HandHeldLegend/HHL-GameCube-Parts/Triggers/Front View.png

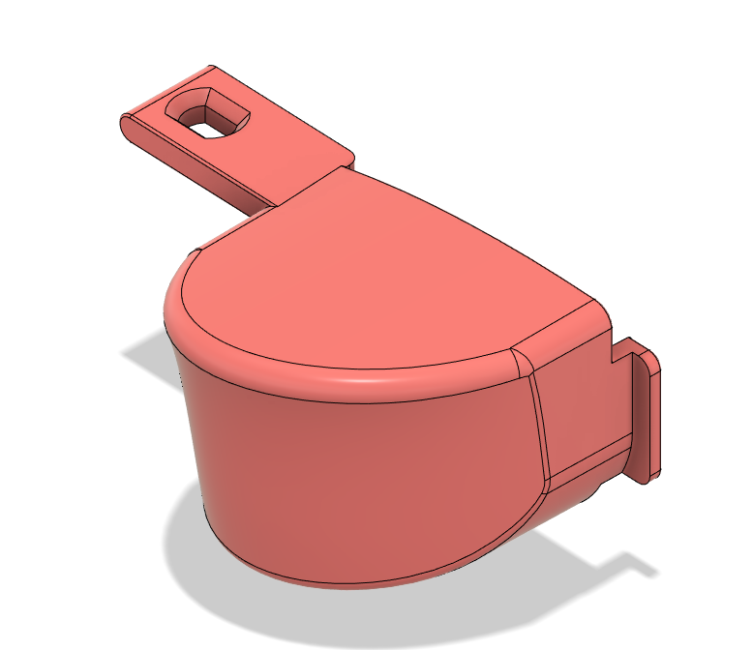
Triggers/Front View.png
