HandHeldLegend/HHL-GameCube-Parts/Buttons/X Button.step

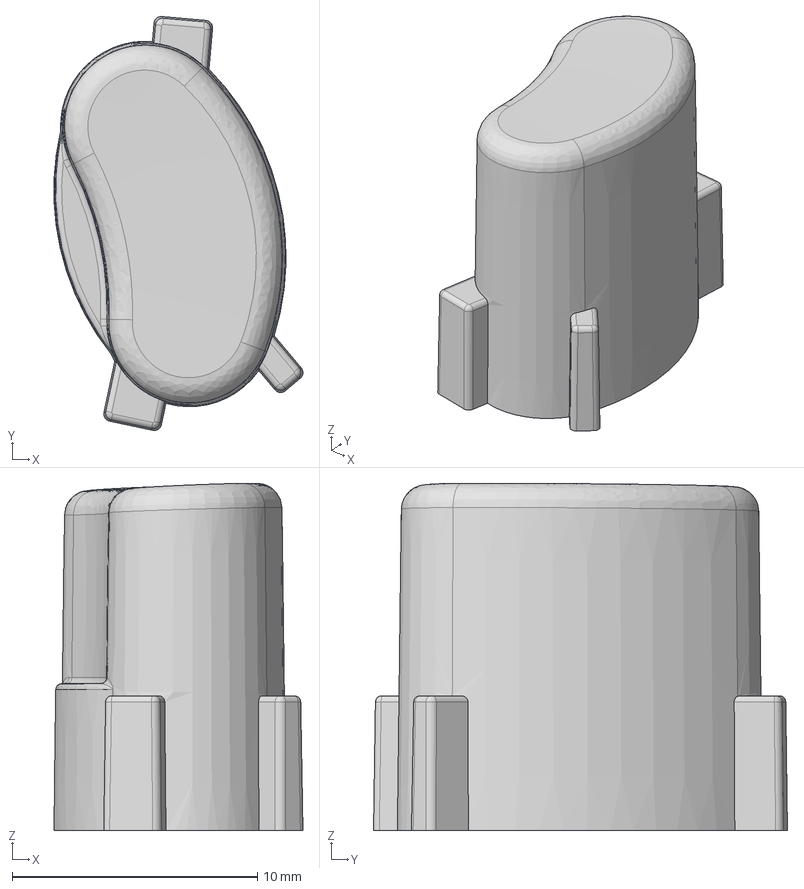
[picture p22: CAD file, 2023-12-15]
Buttons/X Button.step
10.2 x 16.9 x 14.2 mm
