HandHeldLegend/HHL-GameCube-Parts/GC Ultimate/GatePlate Octagon.step

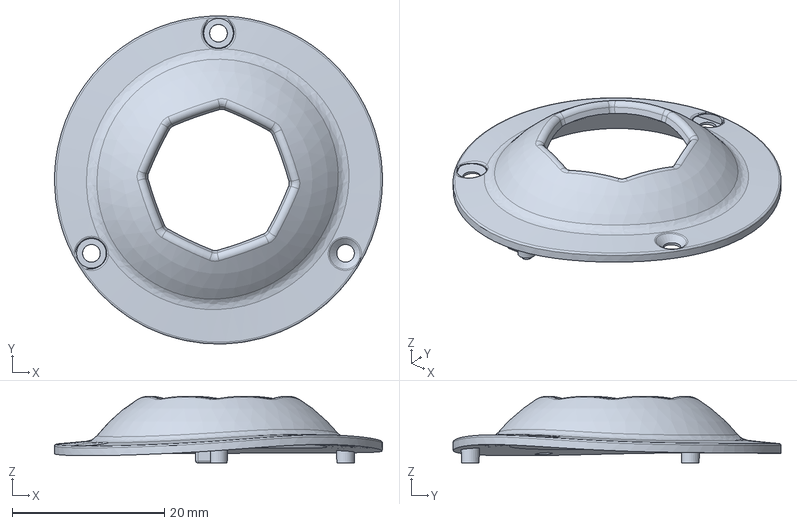
[picture p23: CAD file, 2023-12-01]
GC Ultimate/GatePlate Octagon.step
43.0 x 43.0 x 9.21 mm
