HandHeldLegend/HHL-GameCube-Parts/Buttons/Start Button.step

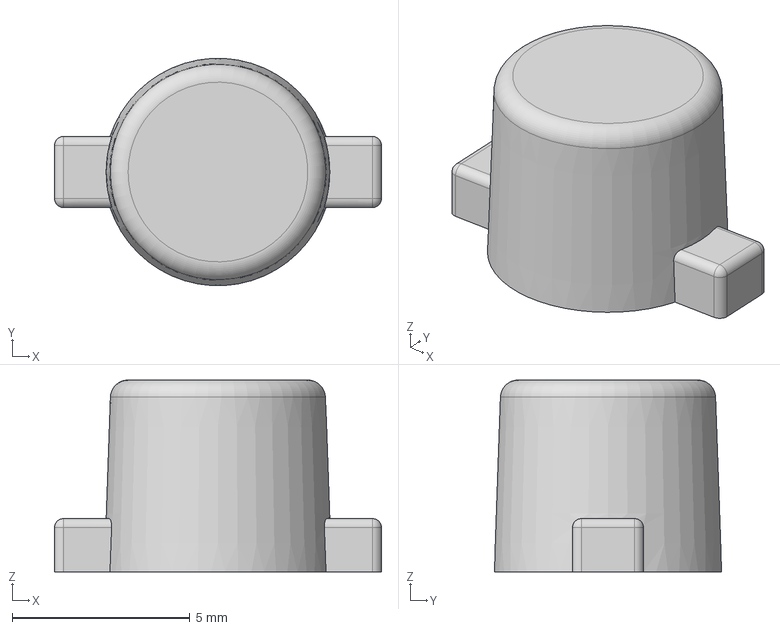
[picture p24: CAD file, 2023-12-15]
Buttons/Start Button.step
9.20 x 6.39 x 5.40 mm
