HandHeldLegend/HHL-GameCube-Parts/Buttons/Y Button.step

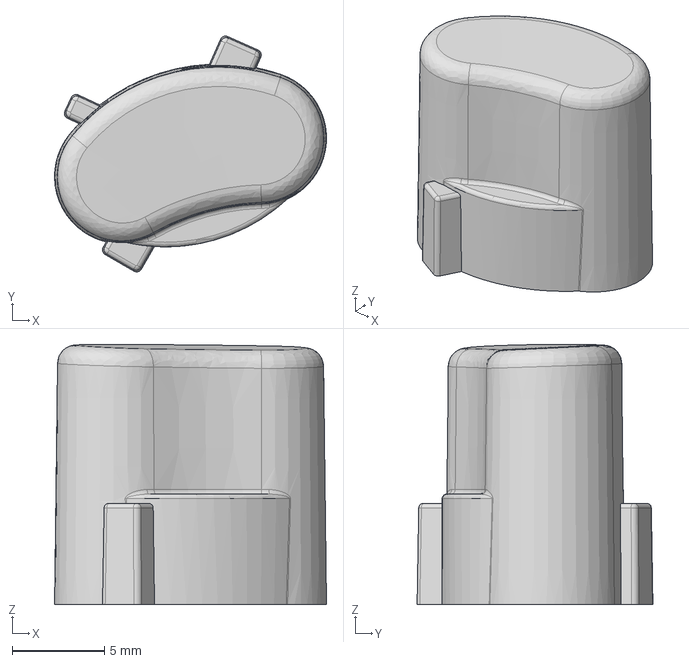
[picture p25: CAD file, 2023-12-15]
Buttons/Y Button.step
14.8 x 12.8 x 14.1 mm
