HandHeldLegend/HHL-GameCube-Parts/Buttons/D-Pad Button.step

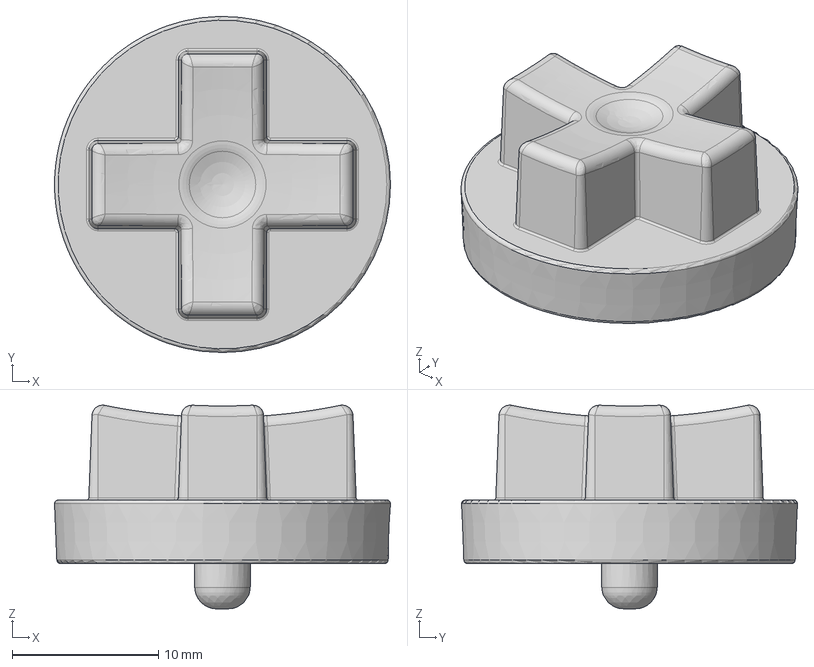
[picture p26: CAD file, 2023-12-14]
Buttons/D-Pad Button.step
23.0 x 23.0 x 13.9 mm
